tskauli/MorseKey/DSC04532.JPG

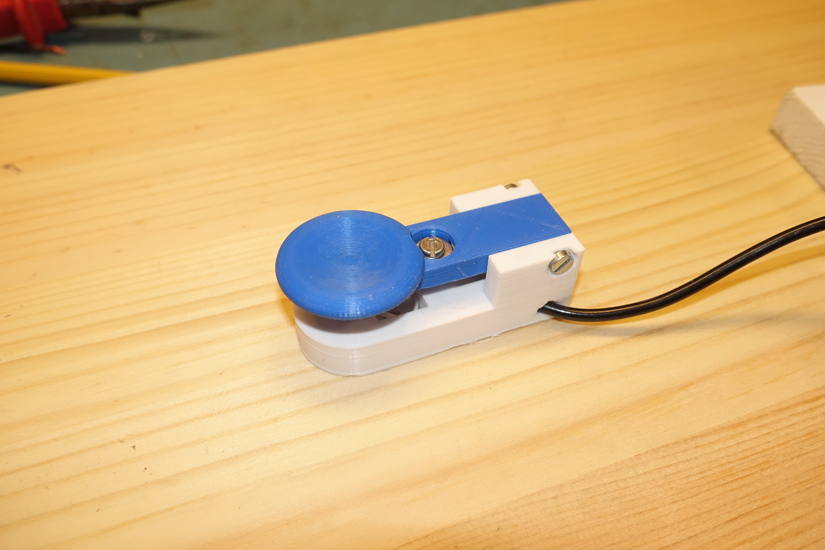
DSC04532.JPG
