tskauli/MorseKey/DSC04535.JPG

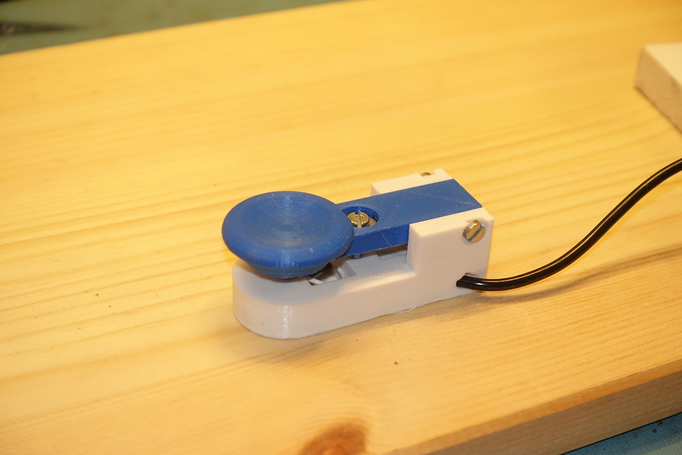
DSC04535.JPG
